LinneweberLab/Mathejczyk_2024_eLife_Individuality/Stripe Stimuli/12deg/12degstripe 0deg front.bmp

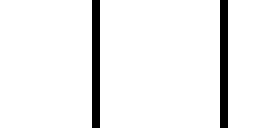
Stripe Stimuli/12deg/12degstripe 0deg front.bmp
