LinneweberLab/Mathejczyk_2024_eLife_Individuality/Stripe Stimuli/12deg/12degstripe 90deg sides b.bmp

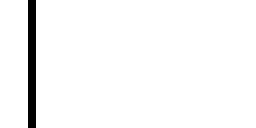
Stripe Stimuli/12deg/12degstripe 90deg sides b.bmp
