LinneweberLab/Mathejczyk_2024_eLife_Individuality/Stripe Stimuli/12deg/BigCylinder 12degstripes.bmp

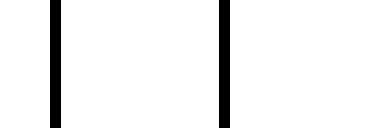
Stripe Stimuli/12deg/BigCylinder 12degstripes.bmp
