LinneweberLab/Mathejczyk_2024_eLife_Individuality/Stripe Stimuli/30deg/30degstripe 0deg front b.bmp

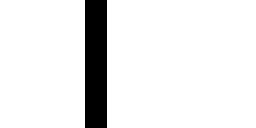
Stripe Stimuli/30deg/30degstripe 0deg front b.bmp
