LinneweberLab/Mathejczyk_2024_eLife_Individuality/3D prints/Flight Sim/9b IR filter slot.stl

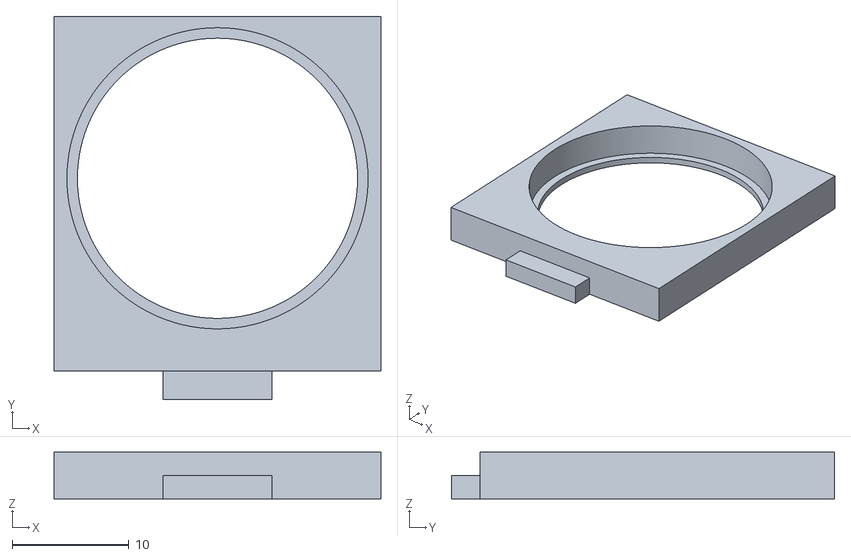
[picture p22: CAD file, 2024-06-28]
3D prints/Flight Sim/9b IR filter slot.stl
28.0 x 32.8 x 4.00
