LinneweberLab/Mathejczyk_2024_eLife_Individuality/3D prints/Flight Sim/6a upper holder.stl

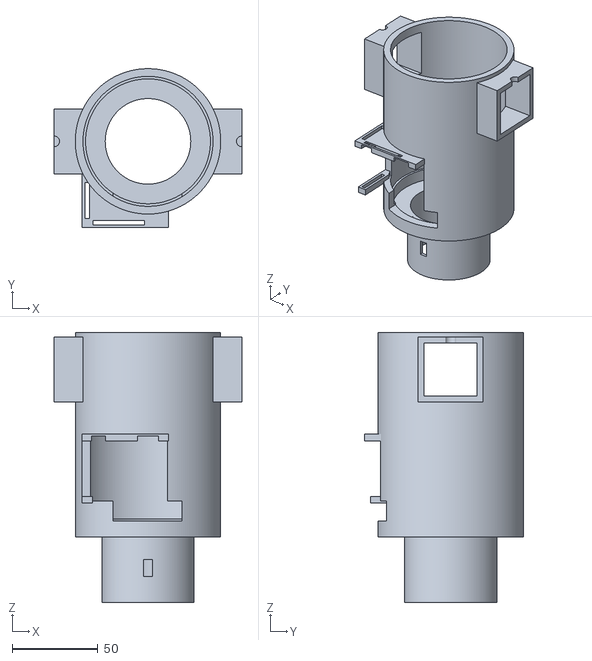
[picture p23: CAD file, 2024-06-28]
3D prints/Flight Sim/6a upper holder.stl
109.8 x 92.8 x 157.8
