LinneweberLab/Mathejczyk_2024_eLife_Individuality/3D prints/Flight Sim/6c optional LED mount upper part.stl

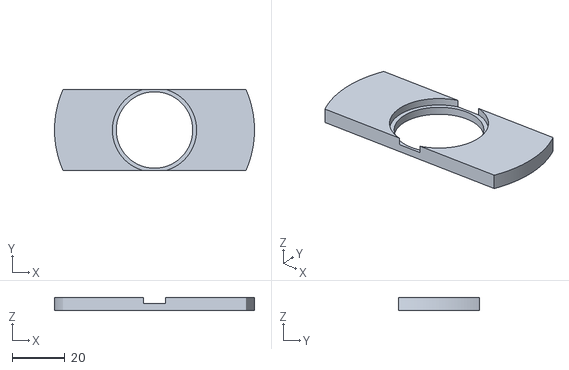
[picture p24: CAD file, 2024-06-28]
3D prints/Flight Sim/6c optional LED mount upper part.stl
76.0 x 30.9 x 5.00
