LinneweberLab/Mathejczyk_2024_eLife_Individuality/3D prints/Flight Sim/9a filter box.stl

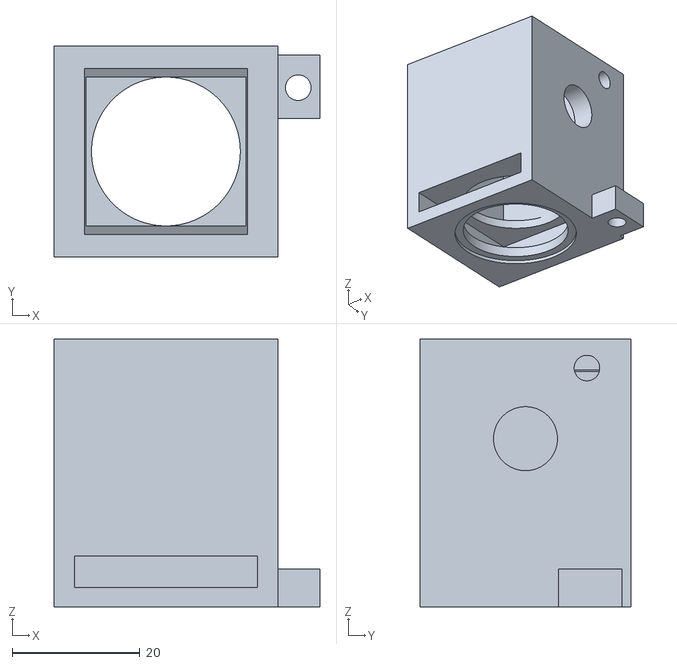
[picture p25: CAD file, 2024-06-28]
3D prints/Flight Sim/9a filter box.stl
41.6 x 33.0 x 41.9
