LinneweberLab/Mathejczyk_2024_eLife_Individuality/3D prints/Flight Sim/7 ring magnet holder.stl

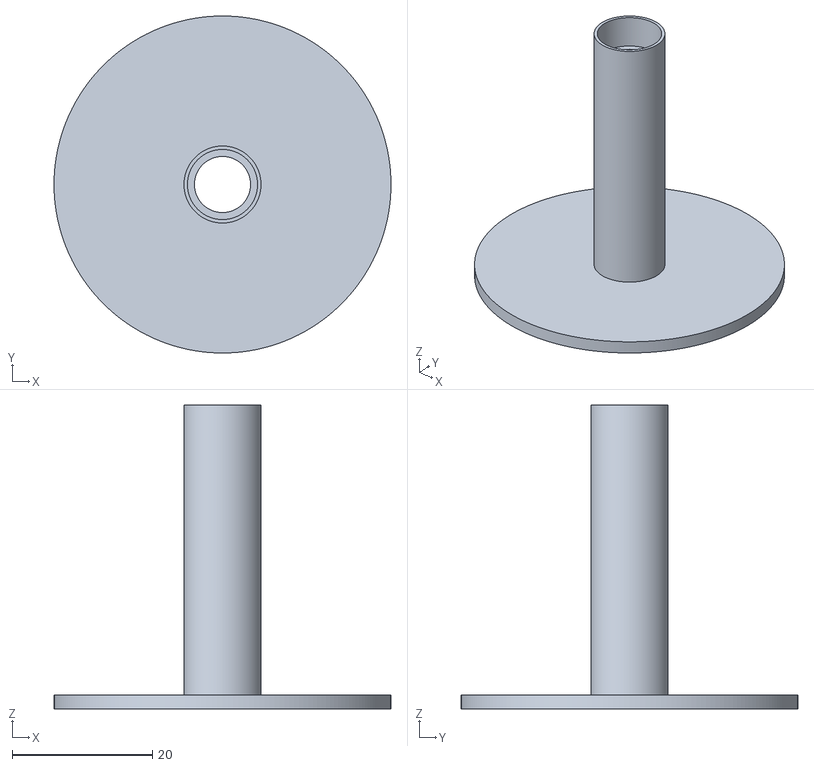
[picture p26: CAD file, 2024-06-28]
3D prints/Flight Sim/7 ring magnet holder.stl
48.1 x 48.1 x 43.3
