LinneweberLab/Mathejczyk_2024_eLife_Individuality/3D prints/Flight Sim/6e optional gear 2 upper part.stl

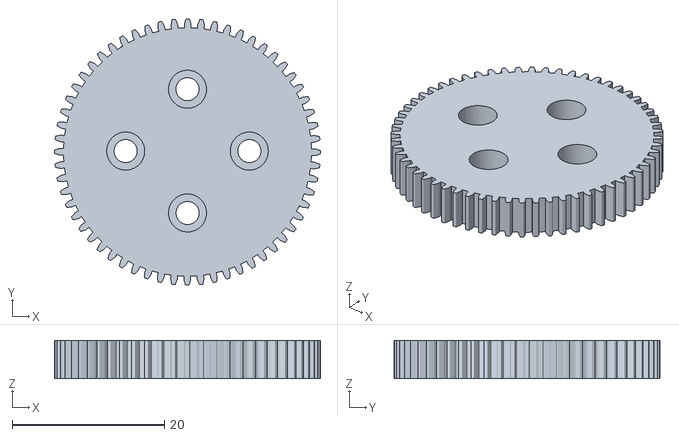
[picture p27: CAD file, 2024-06-28]
3D prints/Flight Sim/6e optional gear 2 upper part.stl
35.0 x 35.0 x 5.00
